Shaurya-ey/SANJAYA-LINK/Cart/amazon2.jpeg

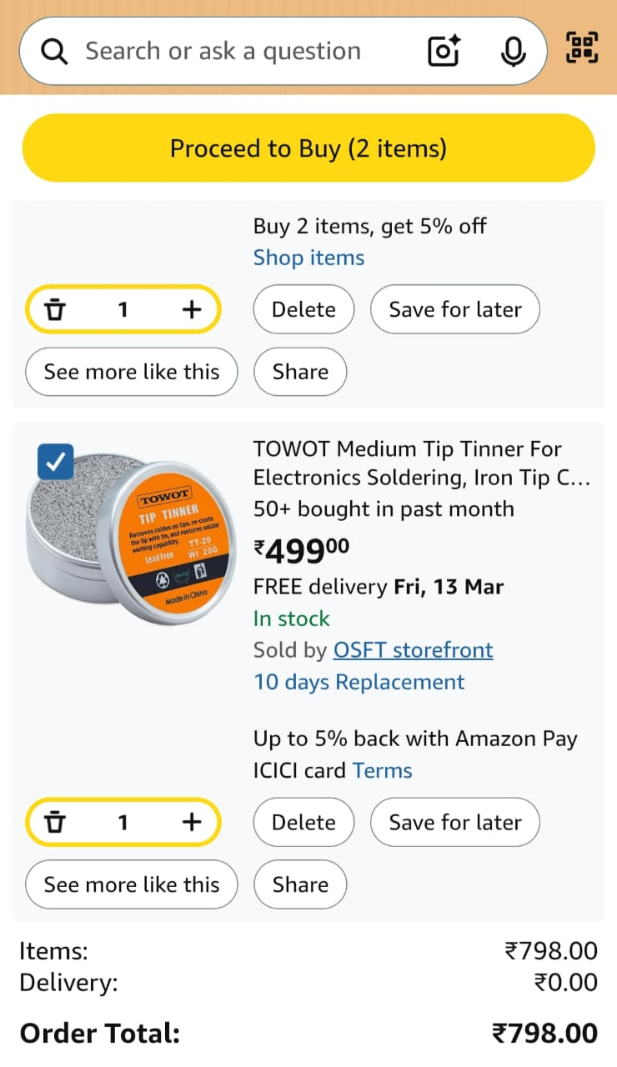
Cart/amazon2.jpeg
