Shaurya-ey/SANJAYA-LINK/Cart/d1.PNG

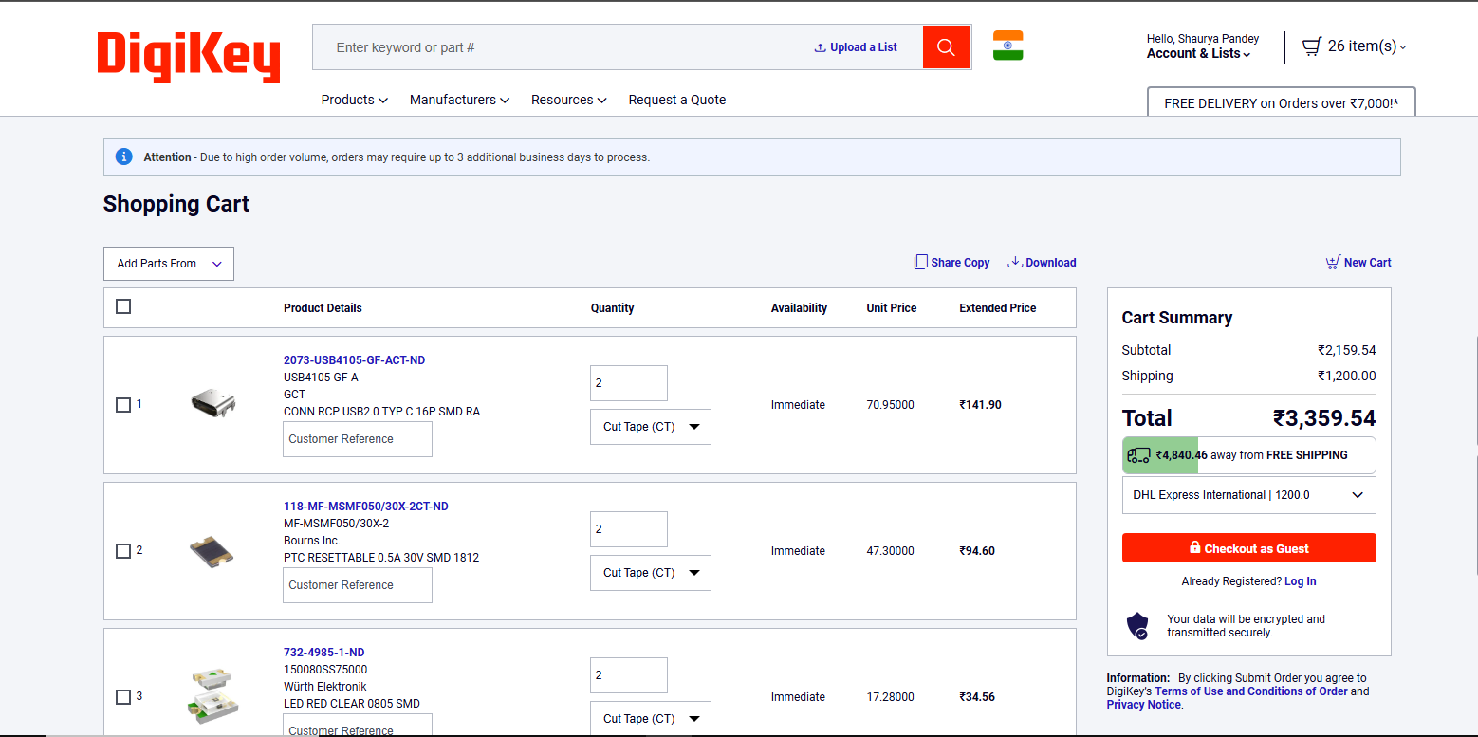
Cart/d1.PNG
