Shaurya-ey/SANJAYA-LINK/Cart/d2.PNG

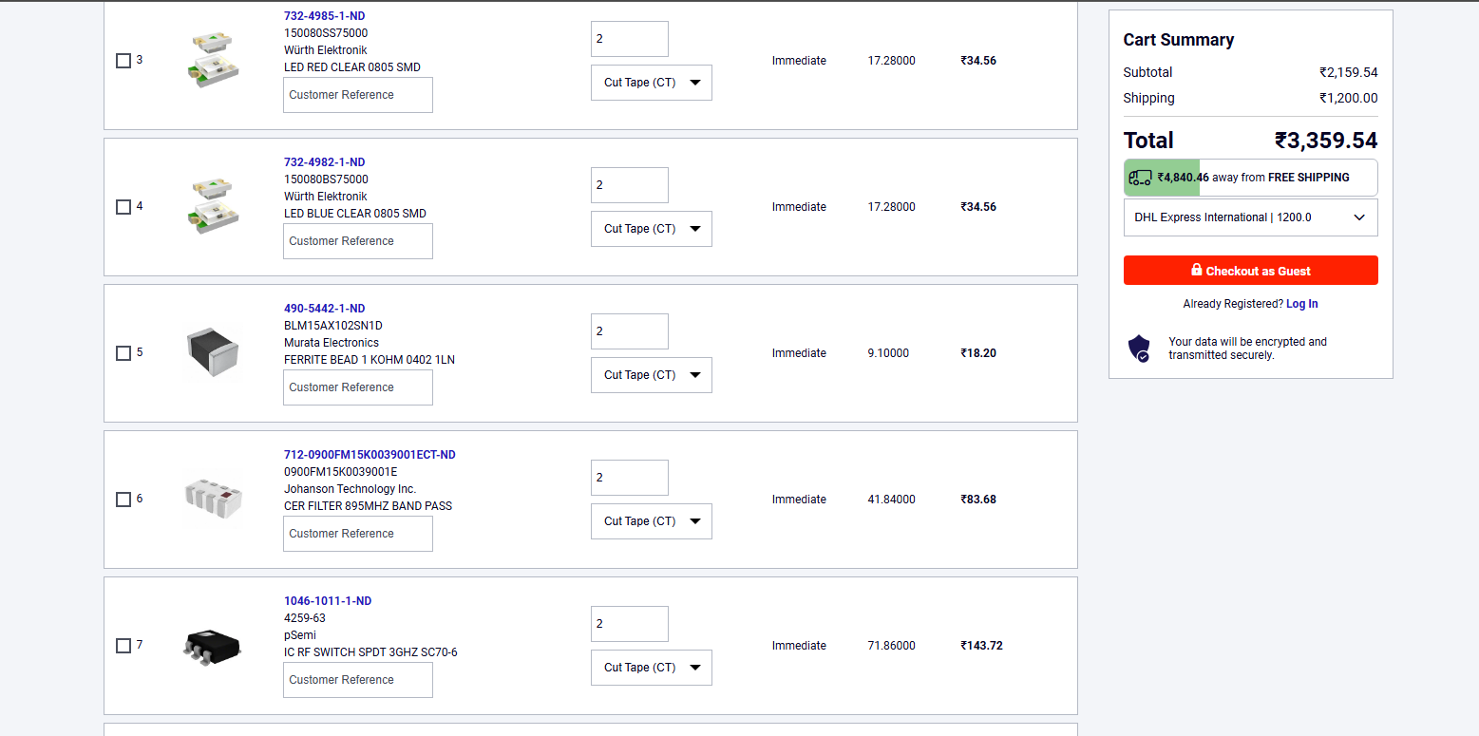
Cart/d2.PNG
