Shaurya-ey/SANJAYA-LINK/Cart/d5.PNG

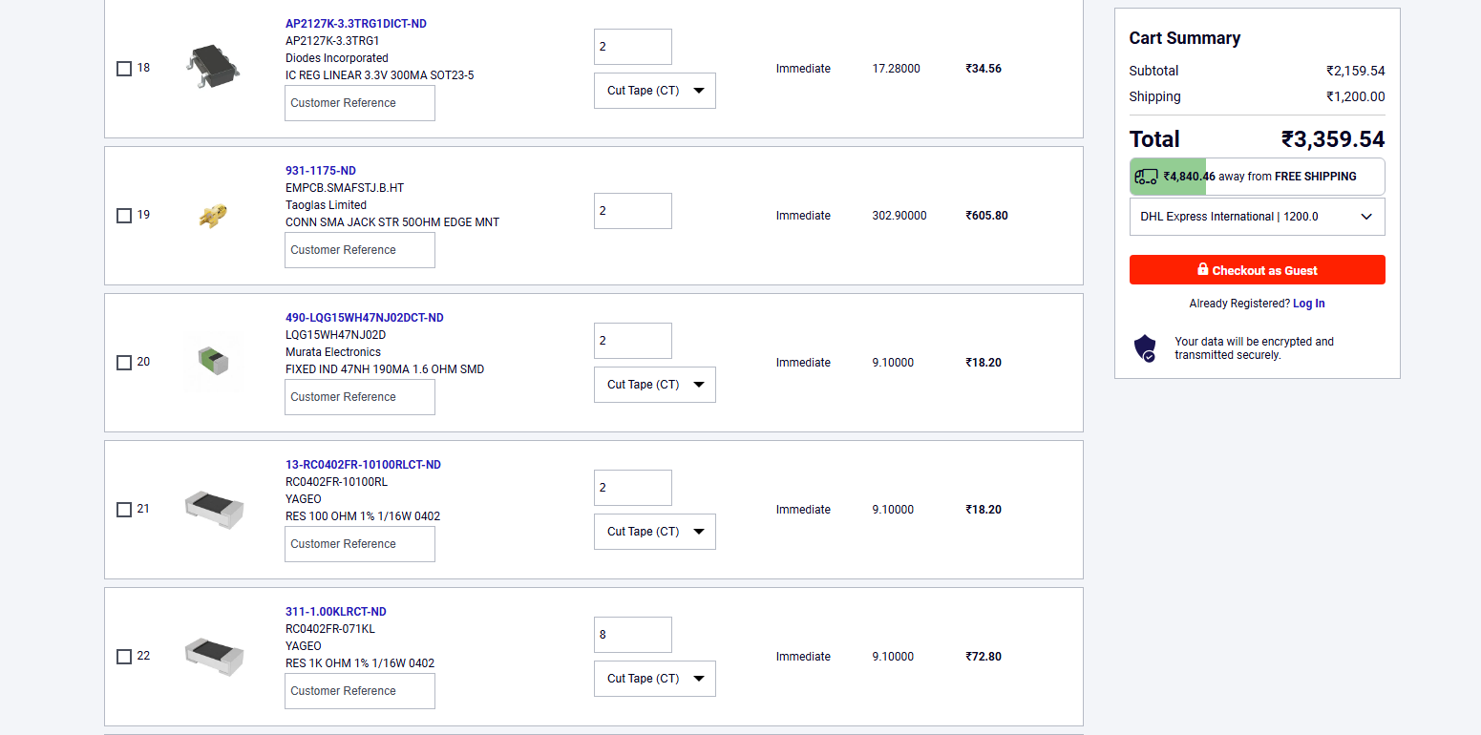
Cart/d5.PNG
