Shaurya-ey/SANJAYA-LINK/Cart/d6.PNG

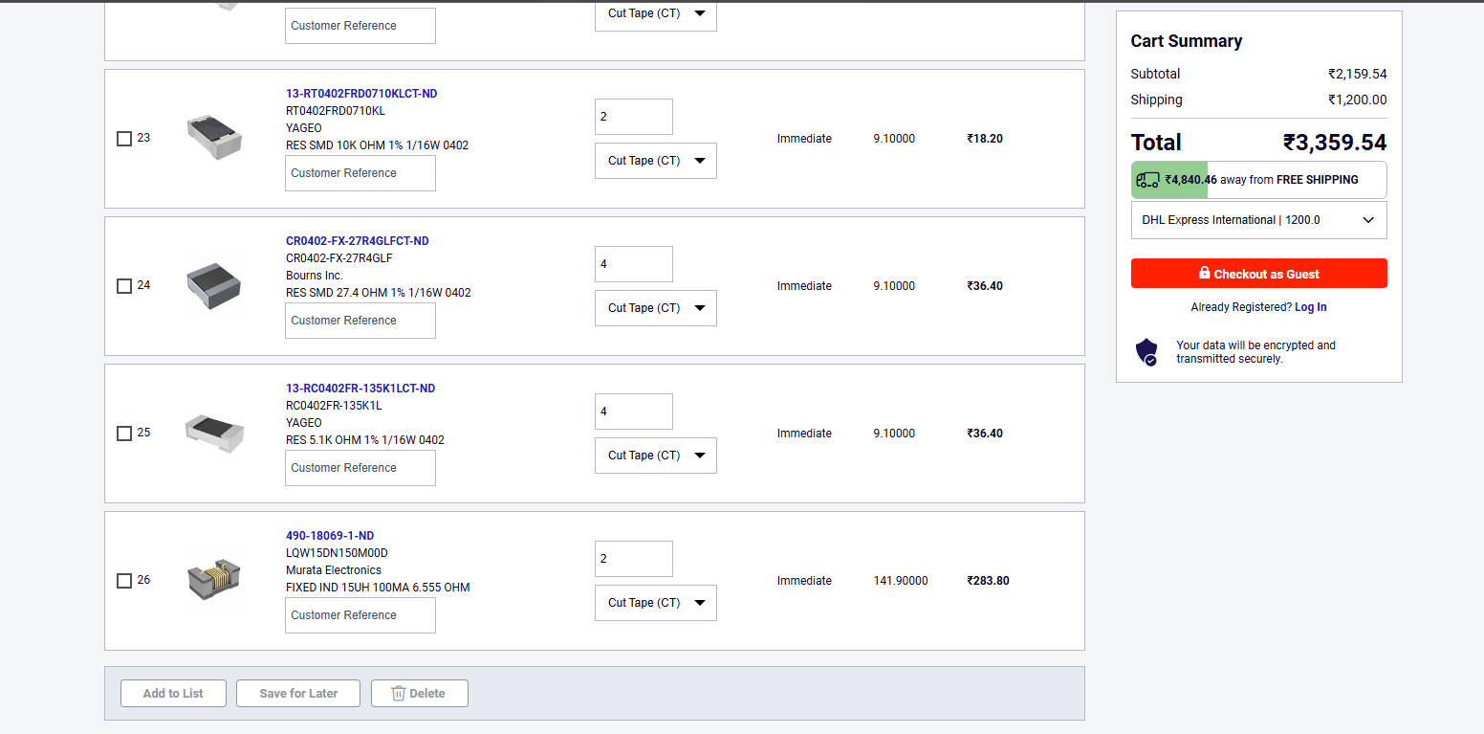
Cart/d6.PNG
