Shaurya-ey/SANJAYA-LINK/Cart/r2.PNG

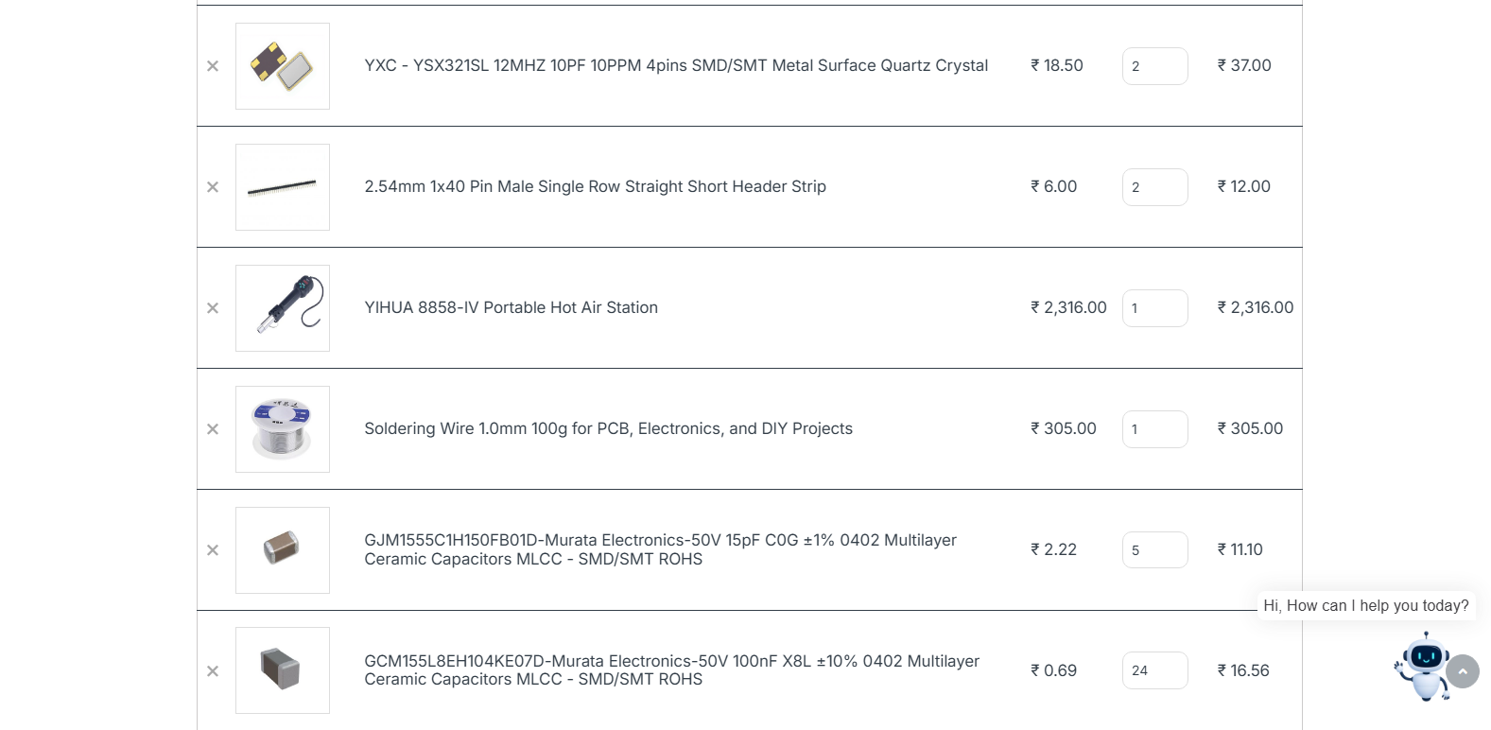
Cart/r2.PNG
