Shaurya-ey/SANJAYA-LINK/Cart/r3.PNG

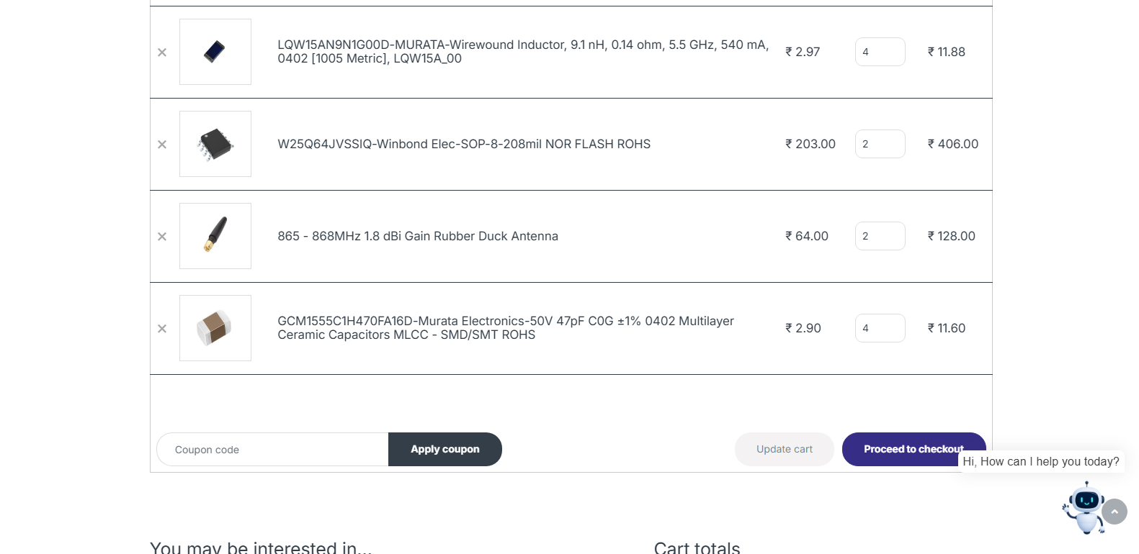
Cart/r3.PNG
