Shaurya-ey/SANJAYA-LINK/Cart/r4.PNG

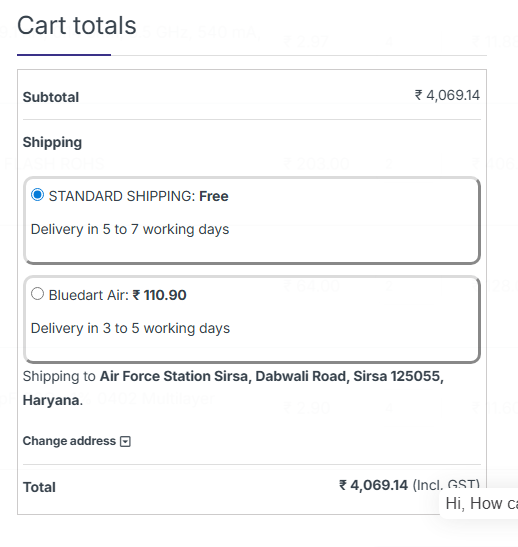
Cart/r4.PNG
